bkifft/zc95/docs/images/BuzzGame.jpg

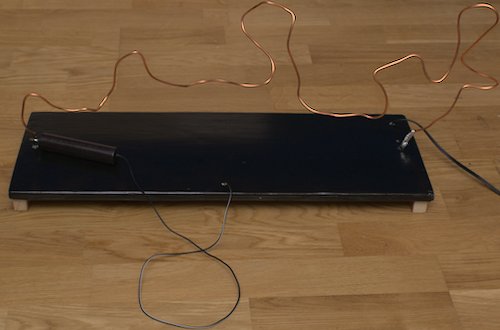
docs/images/BuzzGame.jpg
