bkifft/zc95/docs/images/screen_pattern_audioVirtual3.jpg

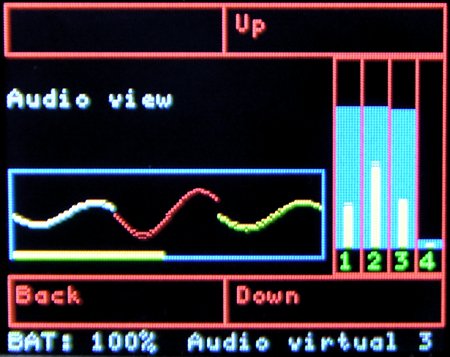
docs/images/screen_pattern_audioVirtual3.jpg
