bkifft/zc95/docs/images/screen_pattern_audioWave.jpg

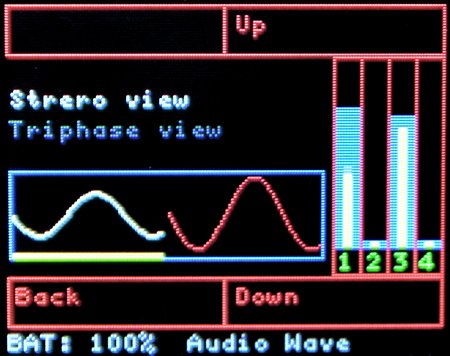
docs/images/screen_pattern_audioWave.jpg
