bkifft/zc95/docs/images/screen_ra_ap.jpg

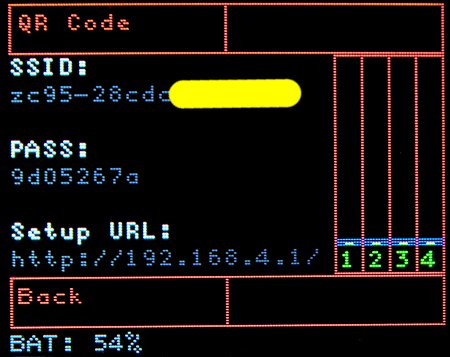
docs/images/screen_ra_ap.jpg
