bkifft/zc95/docs/images/gui_debug_window.png

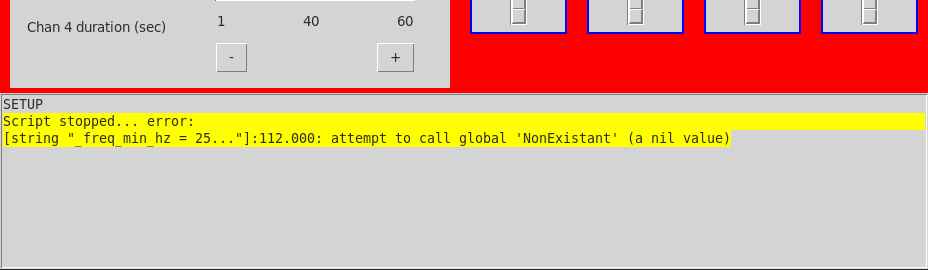
docs/images/gui_debug_window.png
