bkifft/zc95/source/zc95/CSavedSettings.h

#ifndef _CSAVEDSETTINGS_H
#define _CSAVEDSETTINGS_H

#include "CEeprom.h"
#include "CChannel_types.h"

#define EEPROM_SIZE      512 // EEPROM is 4Kbit
#define EEPROM_MAGIC_VAL  85 // If this is in setting::EepromInit, assume the eeprom has been initialised

#define EEPROM_CHANNEL_COUNT 10 // Maximum number of configuerd channels that can be saved. Changing this invalidates EEPROM contents

class CSavedSettings
{
    enum class setting
    {
        EepromInit     =  0, // Contains magic value if eeprom as been initialised
        ChannelType    =  1, // Channel id 0 type
        ChannelIndex   =  2, // Channel id 0 index
        //  ...        = 19     Channel id 9 type
        //  ...        = 20     Channel id 9 index
        LEDBrightness  = 21, // default LED brightness
        PowerStep      = 22, // When using rot encoder for power, how many steps to increase power by for each click (e.g. as power level is 0-1000, 10 would give 100 possible power levels)
        RampUpTimeSecs = 23, // When selecting a routine, how long (in seconds) does the power take to reach the power level set on the front pannel
        AudioGainL     = 24, // Gain for left  channel
        AudioGainR     = 25, // Gain for right channel
        MicPreAmp      = 26, // Mic pre-amp enabled
        MicPower       = 27, // Mic power enabled
        Audio          = 28, // Audio setting: Auto/no gain/off
        Debug          = 29, // Debugging output destination
    
        // Collar config
        Collar0IdLow   = 30,
        Collar0IdHigh  = 31,
        Collar0Chan    = 32,
        Collar0Mode    = 33,
       // not used     = 34
       // Collar1IdLow = 35
       // ...
       // Collar9Mode  = 78
       // not used     = 79

        AuxPort        = 80,  // Aux port usage - Audio or Serial
        WifiSSID       = 81,  // SSID to connect to. 32 characters/bytes + null
        WifiPSK        = 114, // Password, 64 characters + null
        WiFiConfigured = 179, // Set to EEPROM_MAGIC_VAL if wifi configured. Anything else means not configured.
        WifiApPsk      = 180, // Auto-generated AP PSK. 16 characters + NULL
        WifiApPskEnd   = 196  //
     // <next>         = 197 
    };

    public:
        struct channel_selection
        {
            CChannel_types::channel_type type;
            uint8_t index;
        };

        struct collar_config
        {
            uint16_t id;
            uint8_t channel;
            uint8_t mode;
        };

        // Possible options for various saved settings 
        enum class setting_audio
        {
            AUTO     = 0,   // Enable audio logic if digipot found, disable otherwise
            NO_GAIN  = 1,   // Enable audio logic even if digipot not found, but disable setting of gain which requires digipot
            OFF      = 2    // Disable audio logic even if digipot is found
        };

        enum class setting_debug
        {
            ACC_PORT = 0,  // Output debugging info on accessory port
            AUX_PORT = 1,  // Output debugging info on aux port
            OFF      = 2   // Disable debugging output
        };

        enum class setting_aux_port_use
        {
            AUDIO  = 0, // Aux port is routed to ADC if audio board present (same as SERIAL if not present)
            SERIAL = 1  // Aux port is routed to uart0
        };

        CSavedSettings(CEeprom *eeprom);
        ~CSavedSettings();
        void save();

        // Channel
        channel_selection get_channel(uint8_t channel_id);
        void set_channel(channel_selection chan, uint8_t channel_id);

        // LED brightness        
        uint8_t get_led_brightness();
        void set_led_brightness(uint8_t led_brightness_percent);

        // Power level step interval
        uint8_t get_power_step_interval();
        void set_power_step_interval(uint8_t power_step);

        // Power ramp up time, seconds
        uint8_t get_ramp_up_time_seconds();
        void set_ramp_up_time_seconds(uint8_t time_secs);

        // Gain for audio input
        uint8_t get_audio_gain_left();
        uint8_t get_audio_gain_right();
        void set_audio_gain_left(uint8_t gain);
        void set_audio_gain_right(uint8_t gain);

        // Mic pre amp. Needs to be turned on to use a microphone on the audio input (line level with it off)
        bool get_mic_preamp_enabled();
        void set_mic_preamp_enabled(bool enabled);

        // Enable mic power. Needs to be on (along with the mic preamp) to use electret microphones
        bool get_mic_power_enabled();
        void set_mic_power_enabled(bool enabled);

        setting_audio get_audio_setting();
        void set_audio_setting(setting_audio setting);

        setting_debug get_debug_dest();
        void set_debug_dest(setting_debug setting);

        // Aux port use
        setting_aux_port_use get_aux_port_use();
        void set_aux_port_use(setting_aux_port_use setting);

        // Wifi credentials. Returns true if credentials returned (wifi already configured)        
        bool get_wifi_credentials(std::string &out_ssid, std::string &out_password);
        bool set_wifi_credentials(std::string ssid, std::string password); // Returns true if saved, false otherwise (e.g. too long)
        void clear_wifi_credentials();
        bool wifi_is_configured();

        // Wifi AP mode psk. Autogenerated on first run. The idea behind storing it is that it's
        // probably annoying if it changes everytime you start AP mode.
        bool get_wifi_ap_psk(std::string &out_psk);
        bool set_wifi_ap_psk(std::string psk);
        void clear_saved_ap_psk();

        // Collar
        bool get_collar_config(uint8_t collar_id, struct collar_config &collar_conf);
        bool set_collar_config(uint8_t collar_id, struct collar_config &collar_conf);


        void eeprom_initialise();
    private:
        bool eeprom_initialised();
        
        void initialise_collar(uint8_t collar_id);
        CEeprom *_eeprom;
        uint8_t _eeprom_contents[EEPROM_SIZE];
};

#endif
