bkifft/zc95/source/zc95/CControlsPortExp.cpp

/*
 * ZC95
 * Copyright (C) 2021  CrashOverride85
 * 
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
 * You should have received a copy of the GNU General Public License
 * along with this program.  If not, see <http://www.gnu.org/licenses/>
 */

#include "CControlsPortExp.h"
#include "globals.h"
#include "CUtil.h"
#include "hardware/gpio.h"
#include <string.h>

/*
 * Deal with port expander U7, which:
 *   - reads input from front pannel buttons A, B, C & D
 *   - is connected to IO1/2/3 on expansion header J17 (for optional audio input board)
 *   - controls the LCD backlight
 * 
 *  P4 - EXPAN_I03 - Mic pre-amp
 *  P5 - EXPAN_I02 - Mic power disable
 *  P6 - EXPAN_I01 - Audio enable (relay)
 *  P7 - LCD back light
 */

CControlsPortExp::CControlsPortExp(uint8_t address)
{
    _address = address;
    _old_state = 3;
    _last_read = 0;    
    _button_states_at_last_check = 0;
    memset(_last_state_change, 0, sizeof(_last_state_change));
}

// Clear any pending input. has_button_been_pressed, etc., should return false after this has been called.
// Can't do this in the constructor as i2c won't have been initialised 
void CControlsPortExp::clear_input()
{
    int retval = i2c_read(__func__, _address, &_last_read, 1, false);
    if (retval == PICO_ERROR_GENERIC || retval == PICO_ERROR_TIMEOUT)
    {
      printf("CControlsPortExp::clear_intput i2c read error!\n");
    }

    _button_states_at_last_check = _last_read;
}

void CControlsPortExp::interrupt()
{
  _interrupt = true;
}

void CControlsPortExp::process(bool always_update)
{
  if (_interrupt || always_update)
  {
    _interrupt = false;
    uint8_t buffer[1];

    int retval = i2c_read(__func__, _address, buffer, 1, false);
    if (retval == PICO_ERROR_GENERIC || retval == PICO_ERROR_TIMEOUT)
    {
      printf("CControlsPortExp::process i2c read error!\n");
      return;
    }
    
    _last_read = buffer[0];
  }
}

bool CControlsPortExp::button_state(enum Button button)
{
    return (_last_read & (1 << (uint8_t)button));
}

bool CControlsPortExp::has_button_state_changed(enum Button button, bool *new_state)
{
  bool button_state_changed;
  bool last_button_state = (_button_states_at_last_check & (1 << (uint8_t)button));
  *new_state = button_state(button);

  button_state_changed = (last_button_state != *new_state);

  if (button_state_changed)
  {
    if (time_us_64() - _last_state_change[(uint8_t)button] < (10 * 1000) ) // 10ms
      return false;
    else
      _last_state_change[(uint8_t)button] = time_us_64();
  }

  if (*new_state)
    _button_states_at_last_check |= (1 << (uint8_t)button);
  else
    _button_states_at_last_check &= ~(1 << (uint8_t)button);

  return button_state_changed;
}

/*
 * Enable microphone pre-amp on audio input board. Massively increases gain. 
 * Also results in mono input only as there is only one mic preamp
 */
void CControlsPortExp::mic_preamp_enable(bool enable)
{
    const int MicPreampEnablePin = 4;
    set_pin_state(MicPreampEnablePin, enable);
}

/*
 * When enabled and audio_input (below) is also enabled, ~3v is supplied via a current 
 * limiting resistor to the ring of the 3.5mm socket to power electret microphones
 */
void CControlsPortExp::mic_power_enable(bool enable)
{
    const int MicPowerDisablePin = 5;
    set_pin_state(MicPowerDisablePin, !enable);
}

/* 
 * Enabled  = 3.5mm socket used for Audio input
 * Disabled = 3.5mm socket used for RS232 serial
 */
void CControlsPortExp::audio_input_enable(bool enable)
{
    if (enable)
      printf("Enabling audio input\n");
    else
      printf("Disabling audio input\n");

    const int AudioInputEnablePin = 6;
    set_pin_state(AudioInputEnablePin, enable);
}

void CControlsPortExp::set_lcd_backlight(bool on)
{
    const int BackLightPin = 7;
    set_pin_state(BackLightPin, on);
}

int CControlsPortExp::set_pin_state(uint8_t pin, bool state)
{
    if (state)
        _data_out |= (1 << pin);
    else
        _data_out &= ~(1 << pin);

    int retval = i2c_write(__func__, _address, &_data_out, 1, false);
    if (retval == PICO_ERROR_GENERIC || retval == PICO_ERROR_TIMEOUT)
    {
        printf("CControlsPortExp::set_pin_state i2c write error! (%d)\n", retval);
    }

    return retval;
}
