bkifft/zc95/source/zc95/core1/Core1Messages.h

#ifndef _CCORE1MESSAGES_H
#define _CCORE1MESSAGES_H

#include "pico/mutex.h"
#include <inttypes.h>

// Messages from core0 to core1
#define MESSAGE_ROUTINE_LOAD                  1
#define MESSAGE_ROUTINE_MIN_MAX_CHANGE        2
#define MESSAGE_ROUTINE_MULTI_CHOICE_CHANGE   3
#define MESSAGE_ROUTINE_TRIGGER               4
#define MESSAGE_SET_FRONT_PANNEL_POWER        5
#define MESSAGE_TRIGGER_COLLAR                6
#define MESSAGE_ROUTINE_STOP                  7
#define MESSAGE_ROUTINE_SOFT_BUTTON_PUSHED    8
#define MESSAGE_REINIT_CHANNELS               9
#define MESSAGE_AUDIO_THRES_REACHED          10
#define MESSAGE_AUDIO_INTENSITY              11
#define MESSAGE_ROUTINE_MENU_SELECTED        12
#define MESSAGE_CORE1_SUSPEND                13
#define MESSAGE_SET_REMOTE_ACCESS_POWER      14
#define MESSAGE_SET_REMOTE_ACCESS_MODE       15

// messages from core1 to core0
#define MESSAGE_SET_POWER                   100
#define MESSAGE_SET_MAXIMUM_POWER           101

#define MESSAGE_SET_LED_CHAN0               110
#define MESSAGE_SET_LED_CHAN1               111
#define MESSAGE_SET_LED_CHAN2               112
#define MESSAGE_SET_LED_CHAN3               113

#define MESSAGE_SET_ACC_IO_PORT_RESET       120
#define MESSAGE_SET_ACC_IO_PORT1_STATE      121
#define MESSAGE_SET_ACC_IO_PORT2_STATE      122
#define MESSAGE_SET_ACC_IO_PORT3_STATE      123

#define MESSAGE_LUA_SCRIPT_STATE            130

enum class lua_script_state_t { NOT_APPLICABLE = 0, VALID = 1 , INVALID = 2};

union __attribute__((packed)) message
{
    uint32_t msg32;
    uint8_t msg8[4];
};


void messages_init();

struct pulse_message_t 
{
    uint64_t abs_time_us;
    uint8_t  pos_pulse_us;
    uint8_t  neg_pulse_us;
};

enum class text_type_t { PRINT, ERROR };

struct pattern_text_output_t
{
    text_type_t text_type;
    char text[150];
    uint64_t time_generated_us;
};

#endif
