bkifft/zc95/source/zc95/display/CMenuRoutineSelection.cpp

/*
 * ZC95
 * Copyright (C) 2021  CrashOverride85
 * 
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
 * You should have received a copy of the GNU General Public License
 * along with this program.  If not, see <http://www.gnu.org/licenses/>
 */

#include "CMenuRoutineSelection.h"
#include "CMenuRoutineAdjust.h"
#include "CMenuSettings.h"
#include "../globals.h"
#include "../core1/output/CFullChannelAsSimpleChannel.h"
#include "../core1/CRoutineOutput.h"

#include <string.h>

CMenuRoutineSelection::CMenuRoutineSelection(
    CDisplay* display, 
    std::vector<CRoutines::Routine> *routines, 
    CGetButtonState *buttons, 
    CSavedSettings *settings, 
    CRoutineOutput *routine_output,
    CHwCheck *hwCheck,
    CAudio *audio,
    CAnalogueCapture *analogueCapture,
    CWifi *wifi)
{
    printf("CMenuRoutineSelection() \n");
    _display = display;
    _area = display->get_display_area();
    _routine_disply_list = new COptionsList(display, _area);
    _routines = routines;
    _buttons = buttons;
    _submenu_active = NULL;
    _settings = settings;
    _hwCheck = hwCheck;
    _routine_output = routine_output;
    _audio = audio;
    _analogueCapture = analogueCapture;
    _wifi = wifi;
}

CMenuRoutineSelection::~CMenuRoutineSelection()
{
    printf("~CMenuRoutineSelection() \n");

    if (_routine_disply_list != NULL)
    {
        delete _routine_disply_list;
        _routine_disply_list = NULL;
    }

    if (_submenu_active)
    {
        delete _submenu_active;
        _submenu_active = NULL;
    }
}

void CMenuRoutineSelection::button_released(Button button)
{
    if (_submenu_active)
    {
        _submenu_active->button_released(button);
    }
}

void CMenuRoutineSelection::button_pressed(Button button)
{
    if (_submenu_active)
    {
        _submenu_active->button_pressed(button);
    }
    else
        {
        if (button == Button::A) // Select
        {
            CRoutines::Routine routine = (*_routines)[_routine_disply_list->get_current_selection()];
            _last_selection = _routine_disply_list->get_current_selection();
            set_active_menu(new CMenuRoutineAdjust(_display, routine, _buttons, _routine_output, _audio));
            _routine_output->activate_routine(_routine_disply_list->get_current_selection());
        }

        if (button == Button::B) // "Config"
        {
            set_active_menu(new CMenuSettings(_display, _buttons, _settings, _routine_output, _hwCheck, _audio, _analogueCapture, _wifi));
        }
        
        if (button == Button::C) // "Up"
        {
            _routine_disply_list->up();
        }

        if (button == Button::D) // "Down"
        {
            _routine_disply_list->down();
        }
    }
}

void CMenuRoutineSelection::adjust_rotary_encoder_change(int8_t change)
{
    if (_submenu_active)
        _submenu_active->adjust_rotary_encoder_change(change);
}

void CMenuRoutineSelection::draw()
{
    _routine_disply_list->draw();
}

void CMenuRoutineSelection::show()
{
    _display->set_option_a("Select");
    _display->set_option_b("Config");
    _display->set_option_c("Up");
    _display->set_option_d("Down");

    // Get a list of routines to show
    _routine_disply_list->clear_options();
    int index=0;
    for (std::vector<CRoutines::Routine>::iterator it = _routines->begin(); it != _routines->end(); it++)
    {
        struct routine_conf conf;
        CRoutine* routine = (*it).routine_maker((*it).param);
        routine->get_config(&conf);

        // Add a warning for routines that disable channel isolation
        std::string name;
        if (conf.enable_channel_isolation)
            name = conf.name;
        else
            name = "(!)" + conf.name;

        // Hide audio routies from menu if audio hardware not present. Show everything else.        
        if (!is_audio_routine(conf))
        {
            _routine_disply_list->add_option(name, index);
        }
        else
        {
            if (_audio->get_audio_hardware_state() != audio_hardware_state_t::NOT_PRESENT)
            {
                _routine_disply_list->add_option(name, index);
            }
        }

        index++;
        delete routine;
    }

    // If we've already been in a routine and come back to this menu, pre-select that routine, instead
    // of going back to the top of the list
    if (_last_selection > 0)
    {
        _routine_disply_list->set_selected(_last_selection);
    }
}

// If a routine has any menu item that uses audio, return true
bool CMenuRoutineSelection::is_audio_routine(routine_conf conf)
{
    return (conf.audio_processing_mode != audio_mode_t::OFF);
}
