bkifft/zc95/source/zc624/CMessageProcess.h

#ifndef _CMESSAGEPROCESS_H
#define _CMESSAGEPROCESS_H

#include "config.h"
#include "COutput.h"

class CMessageProcess
{

    public:
        struct message
        {
            uint8_t command;
            uint8_t arg0;
            uint8_t arg1;
            uint8_t arg2;
        };

        enum class command
        {
            Pulse = 0,
            SetPower = 1,
            Poll = 2,
            PowerDown = 3,

            SetFreq = 4,
            SetPulseWitdh = 5,
            SwitchOn = 6,
            SwitchOff = 7
        };

        CMessageProcess(COutput *output);
        ~CMessageProcess();
        void init();

        void loop();

    private:
        COutput *_output;
        void pulse(message msg);
        void set_power(message msg);
        void set_freq(message msg);
        void set_pulse_width(message msg);
        void on(message msg);
        void off(message msg);
        void power_down(message msg);
};

#endif
