bkifft/zc95/source/zc95/core1/CRoutineOutput.h

#ifndef _CROUTINEOUTPUT_H
#define _CROUTINEOUTPUT_H

#include <inttypes.h>
#include <functional>
#include "routines/CRoutine.h"
#include "output/collar/CCollarComms.h"

class CRoutineOutput
{
    // TODO: rework / get rid of this
    public:
        virtual void set_front_panel_power(uint8_t channel, uint16_t power) = 0;
        virtual uint16_t get_output_power(uint8_t channel) = 0;
        virtual uint16_t get_max_output_power(uint8_t channel) = 0;
        virtual uint16_t get_front_pannel_power(uint8_t channel) = 0;
        virtual void set_remote_power(uint8_t channel, uint16_t power) = 0;
        virtual void enable_remote_power_mode() = 0;
        virtual void disable_remote_power_mode() = 0;

        virtual void activate_routine(uint8_t routine_id) = 0;
        virtual void stop_routine() = 0;

        virtual void menu_min_max_change(uint8_t menu_id, int16_t new_value) = 0;
        virtual void menu_multi_choice_change(uint8_t menu_id, uint8_t choice_id) = 0;
        virtual void menu_selected(uint8_t menu_id) = 0;
        virtual void trigger(trigger_socket socket, trigger_part part, bool active) = 0;
        virtual void soft_button_pressed(soft_button button, bool pressed) = 0;
        virtual void loop() {};

        virtual void collar_transmit (uint16_t id, CCollarComms::collar_channel channel, CCollarComms::collar_mode mode, uint8_t power) = 0;
        virtual void reinit_channels();
        virtual void suspend_core1() = 0;
        virtual void audio_threshold_reached(uint16_t fundamental_freq, uint8_t cross_count);
        virtual void audio_intensity_change(uint8_t left_chan, uint8_t right_chan, uint8_t virt_chan = 0);
        virtual lua_script_state_t get_lua_script_state();
        virtual void set_text_callback_function(std::function<void(pattern_text_output_t)> cb);
};

#endif
